k4b3z4/arduino-lavarropas/include/programas.h

#include <Arduino.h>

// *******************************************************************
// ********************** PROGRAMAS **********************************
//
// {k1,k2,k3,k4,k5,k6,0,0}  (10 segundos)
//  |  |  |  |  |  |    |_ beep
//  |  |  |  |  |  |
//  |  |  |  |  |  |______ llenado
//  |  |  |  |  |_________ vaciado
//  |  |  |__|____________ centrifugado
//  |  |__________________ motor izquierda
//  |_____________________ alimentacion motor
//


 byte PROG_X[] = {

  // 2 minutos vaciado
  B00001000,
  B00001000,
  B01001000,
  B11001000,
  B01001000,
  B00001000,
  B10001000,
  B00001000,
  B01001000,
  B11001000,
  B11001000,
  B11001000,

  // 2 minutos centrifugado vaciado
  B11111000,
  B11111000,
  B11111000,
  B11111000,
  B11111000,
  B11111000,
  B11111000,
  B11111000,
  B11111000,
  B11111000,
  B11111000,
  B11111000,

  // Fin beep
  B01110000,
  B01000001
  
 };



 byte PROG_V[] = {

 // 2 minutos vaciado
  B00001000,
  B00001000,
  B01001000,
  B11001000,
  B01001000,
  B00001000,
  B10001000,
  B00001000,
  B01001000,
  B11001000,
  B01001000,
  B00001001
  
 };

 byte PROG_L[] = {

   // 2 minuto llenado - lavado
   B00000100,
   B00000100,
   B01000100,
   B11000100,
   B01000100,
   B00000100,
   B10000100,
   B00000100,
   B01000100,
   B11000100,
   B01000100,
   B00000101

 };

 byte PROG_K[] = {

   // 10 seg vaciado y llenado
   B00001100,

   // 1 minutos llenado
   B00000100,
   B00000100,
   B00000100,
   B00000100,
   B00000100,
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
  B00000100,
  B00000100,
  B00000100,
  B00000100,
  B10000100,
  B00000100,
  B01000100,
  B11000100,
  B01000100,
  B00000100,
  B10000100,
  B00000100,
  B01000100,
  B11000100,
  B01000100,
  B00000100,
  B10000100,
  B00000100,
  B01000100,
  B11000100,
  B01000100,
  B00000100,

  // 10 minutos lavado
  B10000000,
  B00000000,
  B01000000,
  B11000000,
  B01000000,
  B00000000,
  B10000000,
  B00000000,
  B01000000,
  B11000000,
  B01000000,
  B00000000,
  B10000000,
  B00000000,
  B01000000,
  B11000000,
  B01000000,
  B00000000,
  B10000000,
  B00000000,
  B01000000,
  B11000000,
  B01000000,
  B00000000,
  B10000000,
  B00000000,
  B01000000,
  B11000000,
  B01000000,
  B00000000,
  B10000000,
  B00000000,
  B01000000,
  B11000000,
  B01000000,
  B00000000,
  B10000000,
  B00000000,
  B01000000,
  B11000000,
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

};
